NeuroTinker/NeuroBytes_Interneuron/FIRMWARE/src/HAL.c

#include "HAL.h"
#include <libopencm3/stm32/usart.h>

volatile uint8_t tick = 0;
volatile uint8_t main_tick = 0;
volatile uint8_t read_tick = 0;

volatile uint16_t active_input_pins[NUM_INPUTS] = {[0 ... 10] = 0};

volatile uint8_t active_input_tick[NUM_INPUTS] = {[0 ... 10] = 0};

volatile uint16_t active_output_pins[NUM_INPUTS] = {PIN_AXON1_EX, PIN_AXON2_EX, PIN_AXON3_EX, [NUM_AXONS ... NUM_INPUTS-1] = 0};

volatile uint32_t dendrite_pulses[NUM_DENDS] = {[0 ... NUM_DENDS-1] = 0};
volatile uint8_t dendrite_pulse_count = 0;

/* 

All available input pins are:

PIN_AXON1_IN,
PIN_AXON2_IN,
PIN_AXON3_IN,
PIN_DEND1_EX,
PIN_DEND1_IN, 
PIN_DEND2_EX,
PIN_DEND2_IN,
PIN_DEND3_EX,
PIN_DEND3_IN,
PIN_DEND4_EX,
PIN_DEND4_IN
    
*/

uint32_t active_input_ports[NUM_INPUTS] = {
    PORT_AXON1_IN,
    PORT_AXON2_IN,
    PORT_AXON3_IN,
    PORT_DEND1_EX,
    PORT_DEND1_IN,
    PORT_DEND2_EX,
    PORT_DEND2_IN,
    PORT_DEND3_EX,
    PORT_DEND3_IN,
    PORT_DEND4_EX,
    PORT_DEND4_IN
};

uint32_t active_output_ports[NUM_INPUTS] = {
    PORT_AXON1_EX,
    PORT_AXON2_EX,
    PORT_AXON3_EX,
    PORT_DEND1_EX,
    PORT_DEND1_IN,
    PORT_DEND2_EX,
    PORT_DEND2_IN,
    PORT_DEND3_EX,
    PORT_DEND3_IN,
    PORT_DEND4_EX,
    PORT_DEND4_IN
};

const uint16_t complimentary_pins[NUM_INPUTS] = {
    PIN_AXON1_EX,
    PIN_AXON2_EX,
    PIN_AXON3_EX,
    PIN_DEND1_IN,
    PIN_DEND1_EX,
    PIN_DEND2_IN,
    PIN_DEND2_EX,
    PIN_DEND3_IN,
    PIN_DEND3_EX,
    PIN_DEND4_IN,
    PIN_DEND4_EX
};

const uint32_t complimentary_ports[NUM_INPUTS] = {
    PORT_AXON1_EX,
    PORT_AXON2_EX,
    PORT_AXON3_EX,
    PORT_DEND1_IN,
    PORT_DEND1_EX,
    PORT_DEND2_IN,
    PORT_DEND2_EX,
    PORT_DEND3_IN,
    PORT_DEND3_EX,
    PORT_DEND4_IN,
    PORT_DEND4_EX
};

volatile uint8_t dendrite_pulse_flag[NUM_INPUTS] = {[0 ... NUM_INPUTS-1] = 0};
volatile uint8_t dendrite_ping_flag[NUM_INPUTS] = {[0 ... NUM_INPUTS-1] = 0};

static const uint32_t fingerprint[3] __attribute__((section (".fingerprint"))) __attribute__ ((__used__)) = {
	1, // device id
	2, // firmware version
	0  // unique id
};

bool checkVersion(device_id, version) {return (device_id == fingerprint[0]) && (version = fingerprint[1]) ? true : false;}

void clock_setup(void)
{
	// STM32F0 command:	rcc_clock_setup_in_hsi_out_48mhz();
	rcc_set_sysclk_source(RCC_HSI16);
	rcc_osc_on(RCC_HSI16);
}

void sys_tick_handler(void)
{
    if (++tick >= 50){
		main_tick = 1;
		tick = 0;
	}

	if (read_tick++ >= 2){
		writeBit();
		read_tick = 0;
	}

	readBit(read_tick);
	
    MMIO32((TIM21_BASE) + 0x10) &= ~(1<<0); //clear the interrupt register
}

void systick_setup()
{
    systick_set_clocksource(STK_CSR_CLKSOURCE_EXT);
    STK_CVR = 0;
    //systick_set_reload(2 * xms);
	systick_set_reload(180); //180
    systick_counter_enable();
    systick_interrupt_enable();
}

void gpio_setup(void)
{
	/*	Enable GPIO clocks */
	rcc_periph_clock_enable(RCC_GPIOA);
	rcc_periph_clock_enable(RCC_GPIOB);
	rcc_periph_clock_enable(RCC_GPIOC);

	rcc_peripheral_enable_clock(&RCC_APB2ENR, RCC_APB2ENR_SYSCFGEN); // enable EXTI for PORTB and PORTC


	/*	Set up LED pins, NeuroBytes v1.01:
		Alternative Function Mode with no pullup/pulldown
		Output options: push-pull, high speed
		PIN_R_LED (PB7): AF5, TIM2_CH4
		PIN_G_LED (PA1): AF2, TIM2_CH2
		PIN_B_LED (PB6): AF5, TIM2_CH3
	*/

	gpio_mode_setup(PORT_R_LED, GPIO_MODE_AF, GPIO_PUPD_NONE, PIN_R_LED);
	gpio_mode_setup(PORT_G_LED, GPIO_MODE_AF, GPIO_PUPD_NONE, PIN_G_LED);
	gpio_mode_setup(PORT_B_LED, GPIO_MODE_AF, GPIO_PUPD_NONE, PIN_B_LED);
	gpio_set_output_options(PORT_R_LED, GPIO_OTYPE_PP, GPIO_OSPEED_HIGH, PIN_R_LED);
	gpio_set_output_options(PORT_G_LED, GPIO_OTYPE_PP, GPIO_OSPEED_HIGH, PIN_G_LED);
	gpio_set_output_options(PORT_B_LED, GPIO_OTYPE_PP, GPIO_OSPEED_HIGH, PIN_B_LED);
	gpio_set_af(PORT_R_LED, GPIO_AF5, PIN_R_LED);
	gpio_set_af(PORT_G_LED, GPIO_AF2, PIN_G_LED);
	gpio_set_af(PORT_B_LED, GPIO_AF5, PIN_B_LED);

	
	/* 
		Setup axon pins:
		Axon Excitatory PA10 TIM21_CH1	(temporarily output)
		Axon Inhibitory PA9  TIM21_CH2	(temporarily input)
	*/
	setAsInput(PORT_AXON1_IN, PIN_AXON1_IN);
	setAsOutput(PORT_AXON1_EX, PIN_AXON1_EX);
	setAsInput(PORT_AXON2_IN, PIN_AXON2_IN);
	setAsOutput(PORT_AXON2_EX, PIN_AXON2_EX);
	setAsInput(PORT_AXON3_IN, PIN_AXON3_IN);
	setAsOutput(PORT_AXON3_EX, PIN_AXON3_EX);

	gpio_mode_setup(PORT_IDENTIFY, GPIO_MODE_INPUT, GPIO_PUPD_PULLUP, PIN_IDENTIFY);

	/*
		All dendrites pins are initially set to be inputs.
		Setup dendrite pins:
		Dendrite 1 Excit/Inhib-- PB0/PB1 
	*/

	setAsInput(PORT_DEND1_EX, PIN_DEND1_EX);
	setAsInput(PORT_DEND1_IN, PIN_DEND1_IN);
	setAsInput(PORT_DEND2_EX, PIN_DEND2_EX);
	setAsInput(PORT_DEND2_IN, PIN_DEND2_IN);
	
	setAsInput(PORT_DEND3_EX, PIN_DEND3_EX);
	setAsInput(PORT_DEND3_IN, PIN_DEND3_IN);
	setAsInput(PORT_DEND4_EX, PIN_DEND4_EX);
	setAsInput(PORT_DEND4_IN, PIN_DEND4_IN);


	// enable external interrupts
	nvic_enable_irq(NVIC_EXTI0_1_IRQ);
	nvic_enable_irq(NVIC_EXTI2_3_IRQ);
	nvic_enable_irq(NVIC_EXTI4_15_IRQ);

	nvic_set_priority(NVIC_EXTI0_1_IRQ, 0);
	nvic_set_priority(NVIC_EXTI2_3_IRQ, 0);
	nvic_set_priority(NVIC_EXTI4_15_IRQ, 0);
}

void lpuart_setup(void)
{
	// seutp lpuart interface (for communicating with NID)
	// NOTE: this ocnverts the swd interface to lpuart so debugging with swd will be disables
	rcc_periph_clock_enable(RCC_LPUART1);

	gpio_mode_setup(PORT_LPUART1_RX, GPIO_MODE_AF, GPIO_PUPD_NONE, PIN_LPUART1_RX);
	gpio_mode_setup(PORT_LPUART1_TX, GPIO_MODE_AF, GPIO_PUPD_NONE, PIN_LPUART1_TX);

	gpio_set_af(PORT_LPUART1_RX, GPIO_AF6, PIN_LPUART1_RX);
	gpio_set_af(PORT_LPUART1_TX, GPIO_AF6, PIN_LPUART1_TX);

	USART_BRR(LPUART1) = 0x1A0AA; // 38400 baud
	usart_set_databits(LPUART1, 8);  // USART_CR1_M
	usart_set_stopbits(LPUART1, USART_STOPBITS_1); //USART_CR2_STOP
	usart_set_mode(LPUART1, USART_MODE_TX_RX); //USART_CR1_RE USART_CR1_TE
	usart_set_parity(LPUART1, USART_PARITY_NONE);// USART_CR1_PS USART_CR1_PCE
	usart_set_flow_control(LPUART1, USART_FLOWCONTROL_NONE); // USART_CR3_RTSE USART_CR3_CTSE

	usart_enable(LPUART1); // USART_CR1_UE

	// enable interrupts
	nvic_enable_irq(NVIC_LPUART1_IRQ);
	usart_enable_rx_interrupt(LPUART1); // USART_CR1_RXNEIE
    USART_CR1(LPUART1) |= USART_CR1_RE;
    USART_CR1(LPUART1) |= USART_CR1_TE;
}

void lpuart1_isr(void)
{
    if ((USART_ISR(LPUART1) & USART_ISR_RXNE) != 0){
        readNID();
        USART_RQR(LPUART1) = 0b1000;
        USART_CR1(LPUART1) |= USART_CR1_RE;
    } else if ((USART_ISR(LPUART1) & USART_ISR_TXE) != 0){
        /* USART_CR1(LPUART1) |= USART_CR1_TE; */
        writeNID();
        USART_RQR(LPUART1) |= USART_RQR_TXFRQ;
    }
    USART_ICR(LPUART1) = USART_ISR(LPUART1);
}

void setAsInput(uint32_t port, uint32_t pin)
{
	// setup gpio as an input pin
	gpio_mode_setup(port, GPIO_MODE_INPUT, GPIO_PUPD_PULLDOWN, pin);
	gpio_set_output_options(port, GPIO_OTYPE_PP, GPIO_OSPEED_LOW, pin);

	// setup interrupt for the pin going high
	exti_select_source(pin, port);
	exti_set_trigger(pin, EXTI_TRIGGER_RISING);
	exti_enable_request(pin);
	exti_reset_request(pin);
}

void setAsOutput(uint32_t port, uint32_t pin)
{
	// disable input interrupts
	exti_disable_request(pin);

	// setup gpio as an output pin. pulldown
	gpio_mode_setup(port, GPIO_MODE_OUTPUT, GPIO_PUPD_PULLDOWN, pin);
}

/*
	Each input's ISR tells the communications program that the input is active (getting a message) by setting active_output_pins[i].
*/

void exti0_1_isr(void)
{
	// interrupt handler for pins 0,1 (dend1_in, dend1_ex)
	if ((EXTI_PR & PIN_DEND1_IN) != 0){
		ACTIVATE_INPUT(4, PIN_DEND1_IN);
		EXTI_PR |= PIN_DEND1_IN; // clear interrupt flag
	} else if ((EXTI_PR & PIN_DEND1_EX) != 0){
		ACTIVATE_INPUT(3, PIN_DEND1_EX);
		EXTI_PR |= PIN_DEND1_EX;
	}
}

void exti2_3_isr(void)
{
	// interrupt handler for pins 2,3
	if ((EXTI_PR & PIN_DEND4_IN) != 0){
		ACTIVATE_INPUT(10, PIN_DEND4_IN);
		EXTI_PR |= PIN_DEND4_IN;
	} else if ((EXTI_PR & PIN_DEND4_EX) != 0){
		ACTIVATE_INPUT(9, PIN_DEND4_EX);
		EXTI_PR |= PIN_DEND4_EX;
	}
}

void exti4_15_isr(void)
{
	// interrupt handler for pins 4-15
	if ((EXTI_PR & PIN_DEND3_IN) != 0){
        ACTIVATE_INPUT(8, PIN_DEND3_IN);
		EXTI_PR |= PIN_DEND3_IN;
	} else if ((EXTI_PR & PIN_DEND3_EX) != 0){
        ACTIVATE_INPUT(7, PIN_DEND3_EX);
		EXTI_PR |= PIN_DEND3_EX;
	} else if ((EXTI_PR & PIN_DEND2_IN) != 0){
		// pin 6
        ACTIVATE_INPUT(6, PIN_DEND2_IN);
		EXTI_PR |= PIN_DEND2_IN;
	} else if ((EXTI_PR & PIN_DEND2_EX) != 0){
        ACTIVATE_INPUT(5, PIN_DEND2_EX);
		EXTI_PR |= PIN_DEND2_EX;
	} else if ((EXTI_PR & PIN_AXON2_IN) != 0){
		// pin 9
        ACTIVATE_INPUT(1, PIN_AXON2_IN);
		EXTI_PR |= PIN_AXON2_IN;
	} else if ((EXTI_PR & PIN_AXON3_IN) != 0){
		// pin 10
        ACTIVATE_INPUT(2, PIN_AXON3_IN);
		EXTI_PR |= PIN_AXON3_IN;
	} else if ((EXTI_PR & PIN_AXON1_IN) != 0){
        ACTIVATE_INPUT(0, PIN_AXON1_IN);
		EXTI_PR |= PIN_AXON1_IN;
	}
}

void tim_setup(void)
{
	/* 	Enable and reset TIM2 clock */
	rcc_periph_clock_enable(RCC_TIM2);
	//timer_reset(TIM2);

	// Setup TIM2 interrupts	rcc_set_sysclk_source(RCC_HSI16);
	nvic_enable_irq(NVIC_TIM2_IRQ);
	//nvic_set_priority(NVIC_TIM2_IRQ, 2);
	//rcc_periph_reset_pulse(RST_TIM2);

	/* 	Set up TIM2 mode to no clock divider ratio, edge alignment, and up direction */
	timer_set_mode(TIM2, TIM_CR1_CKD_CK_INT, TIM_CR1_CMS_EDGE, TIM_CR1_DIR_UP);

	/*	Set prescaler to 0: 16 MHz clock */
	timer_set_prescaler(TIM2, 1);

	/* 	Set timer period to 9600: 5 kHz PWM with 9600 steps */
	timer_set_period(TIM2, 9600);

	

	// 	Set TIM2 Output Compare mode to PWM1 on channels 1, 3, and 4 (NeuroBytes v1.01) 
	timer_set_oc_mode(TIM2, TIM_OC2, TIM_OCM_PWM1);
	timer_set_oc_mode(TIM2, TIM_OC3, TIM_OCM_PWM1);
	timer_set_oc_mode(TIM2, TIM_OC4, TIM_OCM_PWM1); 

	// 	Set starting output compare values (NeuroBytes v1.01) 
	timer_set_oc_value(TIM2, TIM_OC2, 0);
	timer_set_oc_value(TIM2, TIM_OC3, 0);
	timer_set_oc_value(TIM2, TIM_OC4, 0); 

	// 	Enable outputs (NeuroBytes v1.01) 
	timer_enable_oc_output(TIM2, TIM_OC2);
	timer_enable_oc_output(TIM2, TIM_OC3);
	timer_enable_oc_output(TIM2, TIM_OC4);

	/*	Enable counter */
	timer_enable_counter(TIM2);

	// Enable TIM2 interrupts (600 us)
	timer_enable_irq(TIM2, TIM_DIER_UIE);
}

void tim2_isr(void)
{
	
	if (timer_get_flag(TIM2, TIM_SR_UIF)){
		timer_clear_flag(TIM2, TIM_SR_UIF);
	}
	
}

void LEDFullWhite(void) 
{
	timer_set_oc_value(TIM2, TIM_OC2, 200);
	timer_set_oc_value(TIM2, TIM_OC3, 200);
	timer_set_oc_value(TIM2, TIM_OC4, 200);
}

void setLED(uint16_t r, uint16_t g, uint16_t b)
{
	if (r <= 1023) 
	{
		timer_set_oc_value(TIM2, TIM_OC4, gamma_lookup[r]);
	}
	else 
	{
		timer_set_oc_value(TIM2, TIM_OC4, 2047);
	}

	if (g <= 1023) 
	{
		timer_set_oc_value(TIM2, TIM_OC2, gamma_lookup[g]);
	}
	else
	{
		timer_set_oc_value(TIM2, TIM_OC2, 2047);
	}

	if (b <= 1023)
	{
		timer_set_oc_value(TIM2, TIM_OC3, gamma_lookup[b]);
	}
	else
	{
		timer_set_oc_value(TIM2, TIM_OC3, 2047);
	}
}

const uint16_t getFingerprint(void)
{
	return fingerprint[0];
}


static const uint16_t gamma_lookup[1024] = {
	/*	Gamma = 2, input range = 0-1023, output range = 0-2047 */
    0,  0,  0,  0,  0,  0,  0,  0,  0,  0,  0,  0,  0,  0,  0,  0,
    1,  1,  1,  1,  1,  1,  1,  1,  1,  1,  1,  1,  2,  2,  2,  2,
    2,  2,  2,  2,  3,  3,  3,  3,  3,  3,  3,  4,  4,  4,  4,  4,
    5,  5,  5,  5,  5,  5,  6,  6,  6,  6,  7,  7,  7,  7,  8,  8,
    8,  8,  9,  9,  9,  9, 10, 10, 10, 10, 11, 11, 11, 12, 12, 12,
   13, 13, 13, 13, 14, 14, 14, 15, 15, 15, 16, 16, 17, 17, 17, 18,
   18, 18, 19, 19, 20, 20, 20, 21, 21, 22, 22, 22, 23, 23, 24, 24,
   25, 25, 25, 26, 26, 27, 27, 28, 28, 29, 29, 30, 30, 31, 31, 32,
   32, 33, 33, 34, 34, 35, 35, 36, 36, 37, 37, 38, 38, 39, 39, 40,
   41, 41, 42, 42, 43, 43, 44, 45, 45, 46, 46, 47, 48, 48, 49, 49,
   50, 51, 51, 52, 53, 53, 54, 55, 55, 56, 57, 57, 58, 59, 59, 60,
   61, 61, 62, 63, 63, 64, 65, 66, 66, 67, 68, 68, 69, 70, 71, 71,
   72, 73, 74, 74, 75, 76, 77, 77, 78, 79, 80, 81, 81, 82, 83, 84,
   85, 85, 86, 87, 88, 89, 90, 90, 91, 92, 93, 94, 95, 96, 96, 97,
   98, 99,100,101,102,103,103,104,105,106,107,108,109,110,111,112,
  113,114,115,115,116,117,118,119,120,121,122,123,124,125,126,127,
  128,129,130,131,132,133,134,135,136,137,138,139,140,142,143,144,
  145,146,147,148,149,150,151,152,153,154,156,157,158,159,160,161,
  162,163,164,166,167,168,169,170,171,173,174,175,176,177,178,180,
  181,182,183,184,186,187,188,189,190,192,193,194,195,197,198,199,
  200,202,203,204,205,207,208,209,210,212,213,214,216,217,218,220,
  221,222,223,225,226,227,229,230,231,233,234,236,237,238,240,241,
  242,244,245,247,248,249,251,252,253,255,256,258,259,261,262,263,
  265,266,268,269,271,272,274,275,277,278,279,281,282,284,285,287,
  288,290,291,293,294,296,298,299,301,302,304,305,307,308,310,311,
  313,315,316,318,319,321,322,324,326,327,329,330,332,334,335,337,
  338,340,342,343,345,347,348,350,352,353,355,357,358,360,362,363,
  365,367,368,370,372,374,375,377,379,380,382,384,386,387,389,391,
  393,394,396,398,400,401,403,405,407,409,410,412,414,416,417,419,
  421,423,425,427,428,430,432,434,436,438,439,441,443,445,447,449,
  451,453,454,456,458,460,462,464,466,468,470,472,473,475,477,479,
  481,483,485,487,489,491,493,495,497,499,501,503,505,507,509,511,
  513,515,517,519,521,523,525,527,529,531,533,535,537,539,541,543,
  545,547,549,552,554,556,558,560,562,564,566,568,570,572,575,577,
  579,581,583,585,587,590,592,594,596,598,600,602,605,607,609,611,
  613,616,618,620,622,624,627,629,631,633,636,638,640,642,644,647,
  649,651,653,656,658,660,663,665,667,669,672,674,676,679,681,683,
  686,688,690,692,695,697,699,702,704,707,709,711,714,716,718,721,
  723,725,728,730,733,735,737,740,742,745,747,749,752,754,757,759,
  762,764,767,769,771,774,776,779,781,784,786,789,791,794,796,799,
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
